svenpetersen1965/C64-PSU-Combi/Rev. 0/pictures/2509_-_Backside.JPG

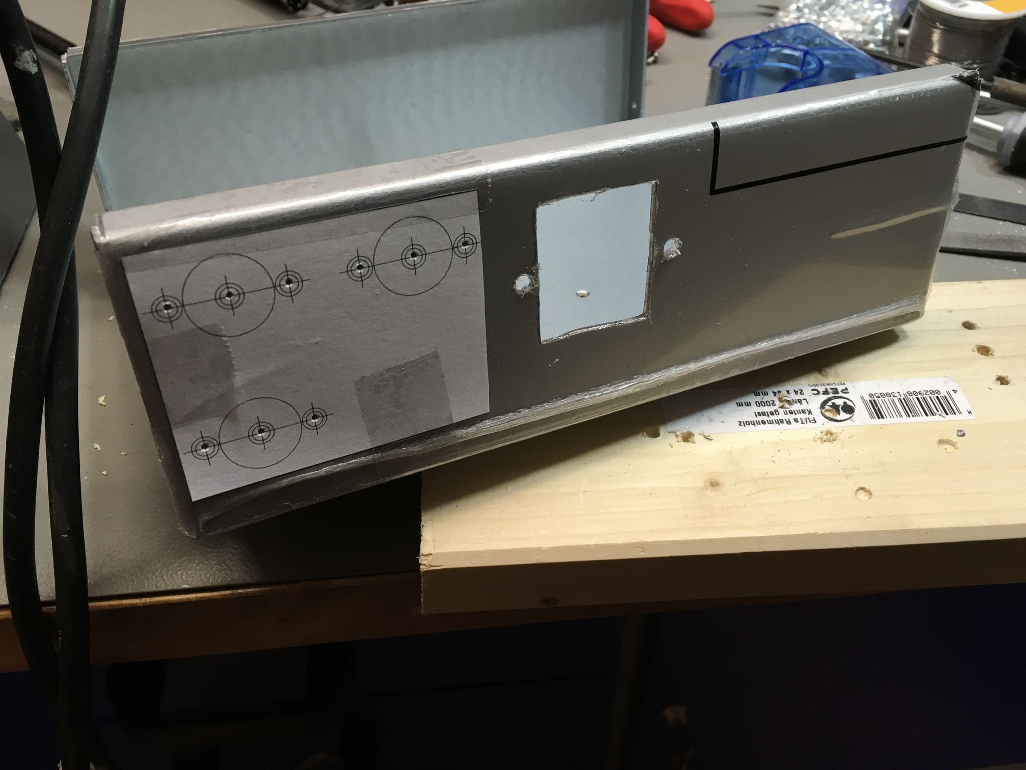
Rev. 0/pictures/2509_-_Backside.JPG
