svenpetersen1965/C64-PSU-Combi/Rev. 0/pictures/2510_-_crimp_tool.JPG

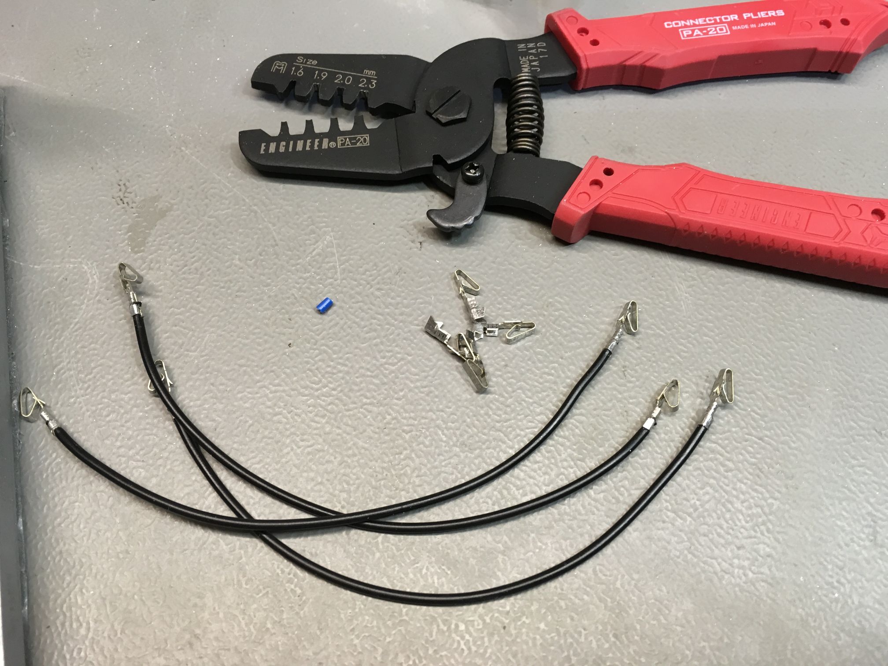
Rev. 0/pictures/2510_-_crimp_tool.JPG
