svenpetersen1965/C64-PSU-Combi/Rev. 0/pictures/2511_-_finished_PSU.JPG

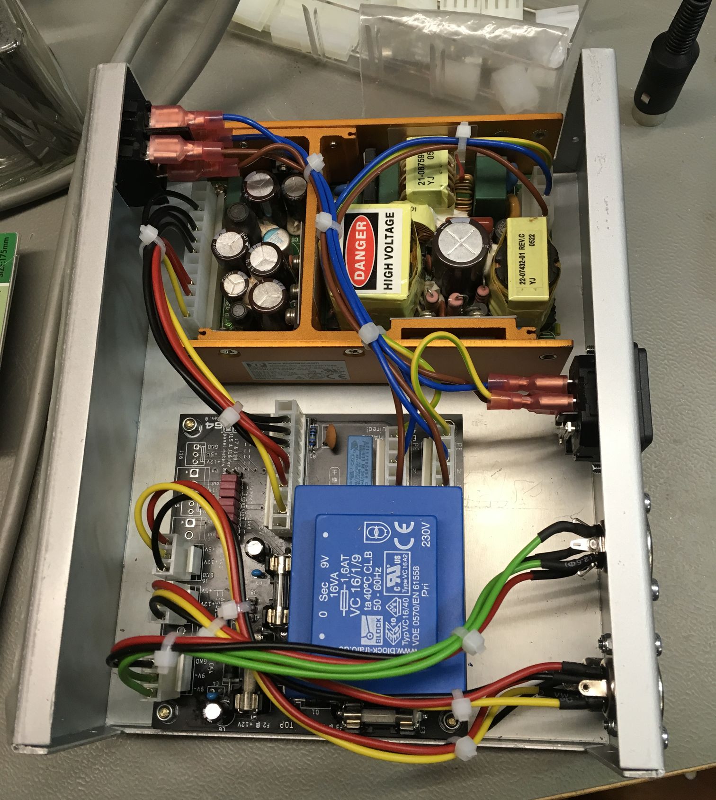
Rev. 0/pictures/2511_-_finished_PSU.JPG
