svenpetersen1965/C64-PSU-Combi/Rev. 0/pictures/2551_-_mounted_PCB.JPG

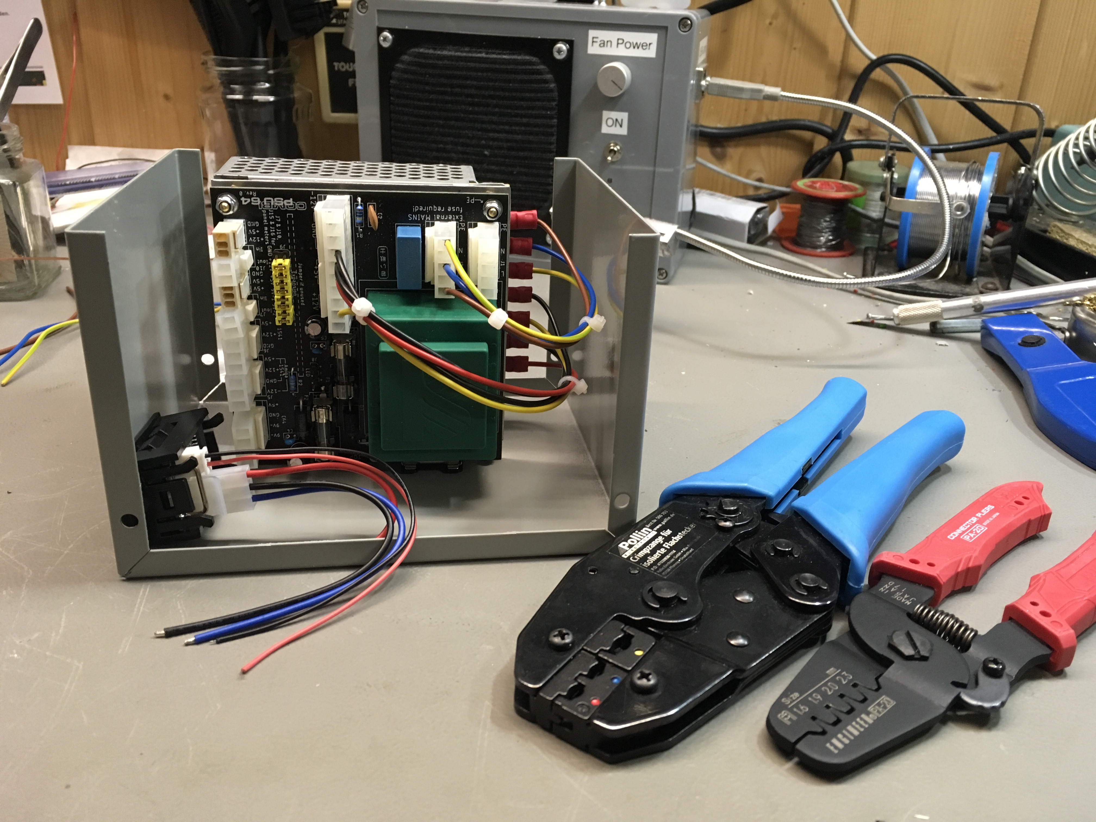
Rev. 0/pictures/2551_-_mounted_PCB.JPG
