svenpetersen1965/C64-PSU-Combi/Rev. 0/pictures/2552_-_mounted_RD_50A.JPG

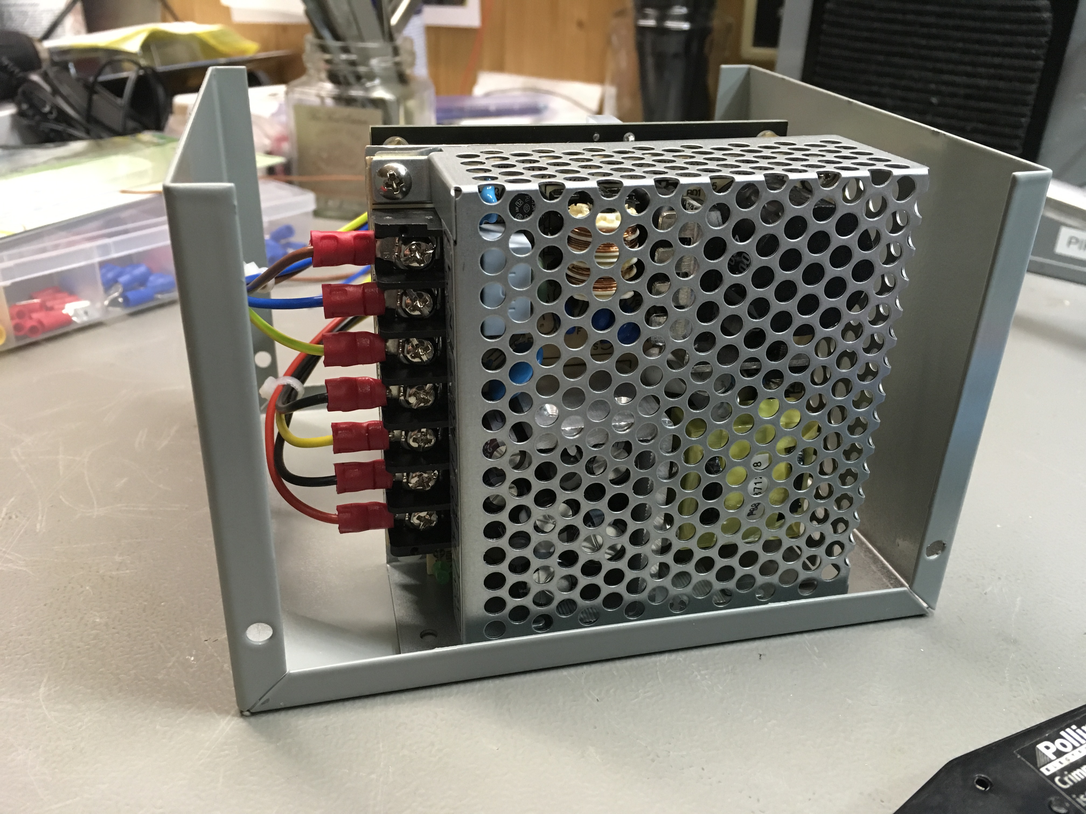
Rev. 0/pictures/2552_-_mounted_RD_50A.JPG
