svenpetersen1965/C64-PSU-Combi/Rev. 0/pictures/2553_-_panel_meters.JPG

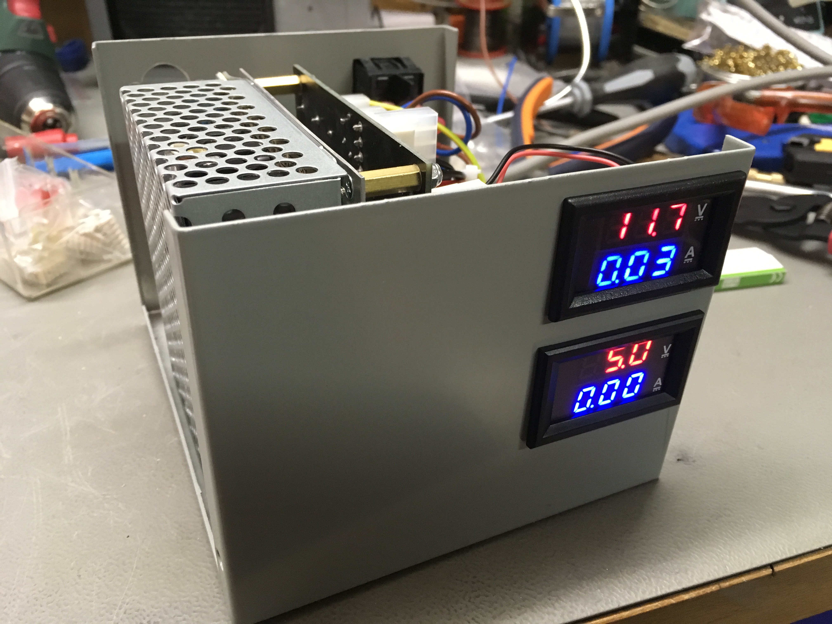
Rev. 0/pictures/2553_-_panel_meters.JPG
