svenpetersen1965/C64-PSU-Combi/Rev. 0/pictures/2554_-_Back_Side.JPG

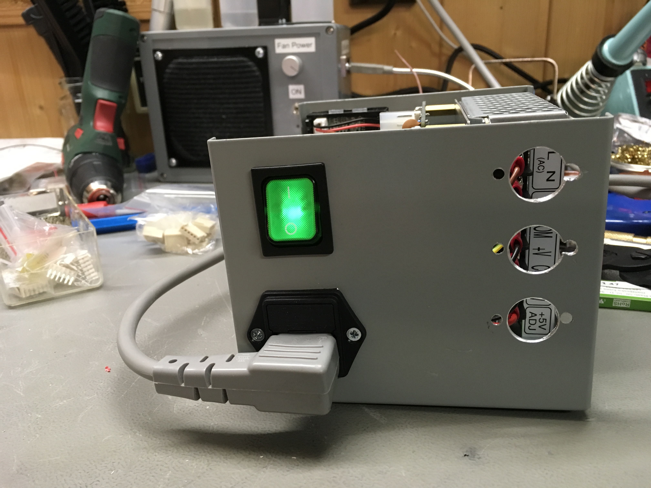
Rev. 0/pictures/2554_-_Back_Side.JPG
