svenpetersen1965/C64-PSU-Combi/Rev. 0/pictures/4061_-_RD50_Adj.JPG

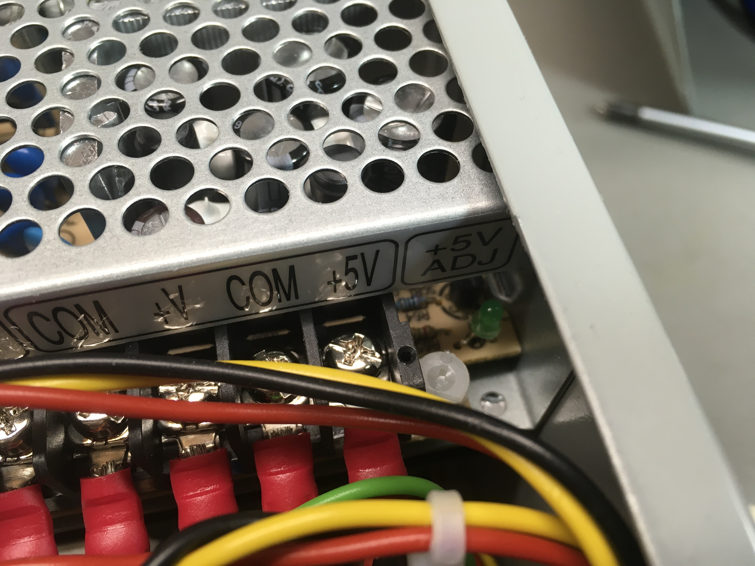
Rev. 0/pictures/4061_-_RD50_Adj.JPG
