svenpetersen1965/C64-PSU-Combi/Rev. 0/pictures/4064_-_bottom_side.JPG

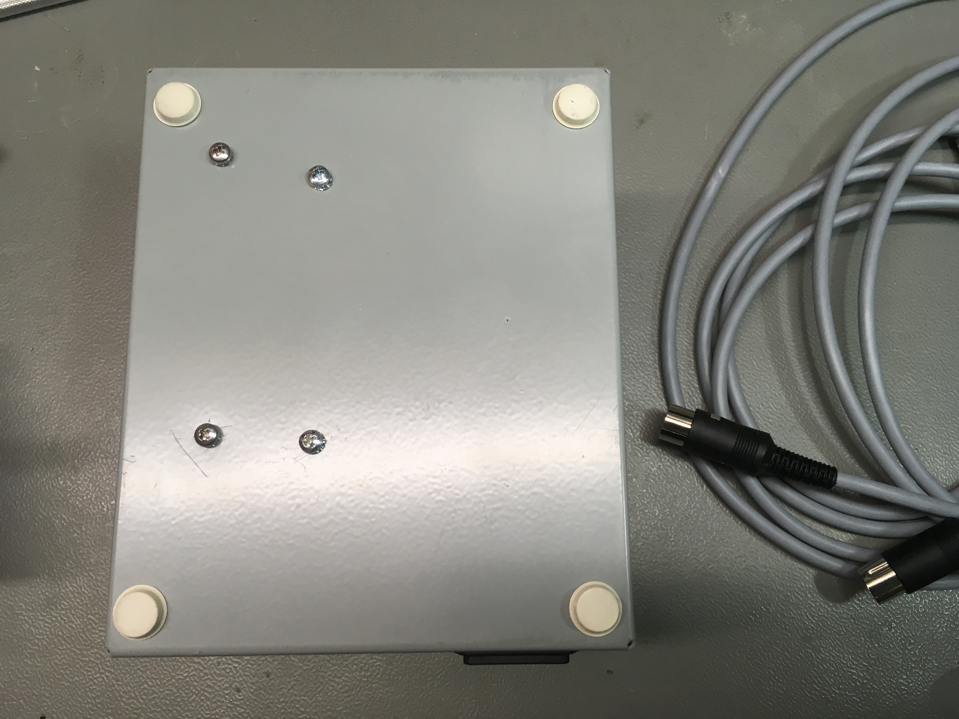
Rev. 0/pictures/4064_-_bottom_side.JPG
