svenpetersen1965/C64-PSU-Combi/Rev. 0/pictures/4066_-_fitting_panel.JPG

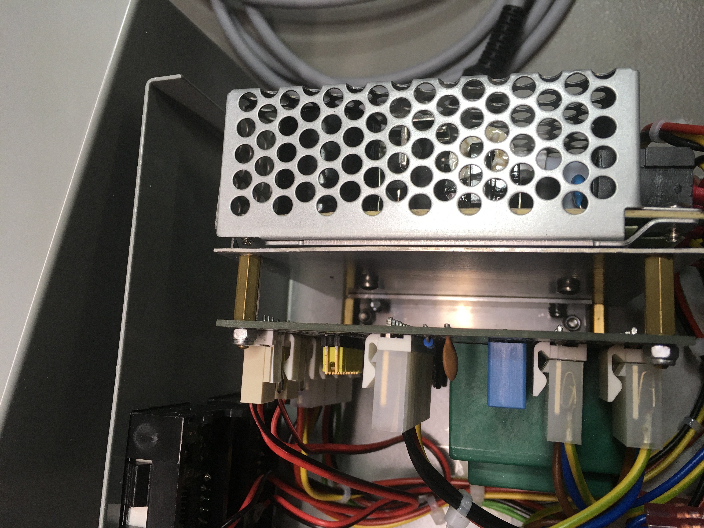
Rev. 0/pictures/4066_-_fitting_panel.JPG
