svenpetersen1965/C64-PSU-Combi/Rev. 1/pictures/C64_Combi_PSU_rev0_drawing.png

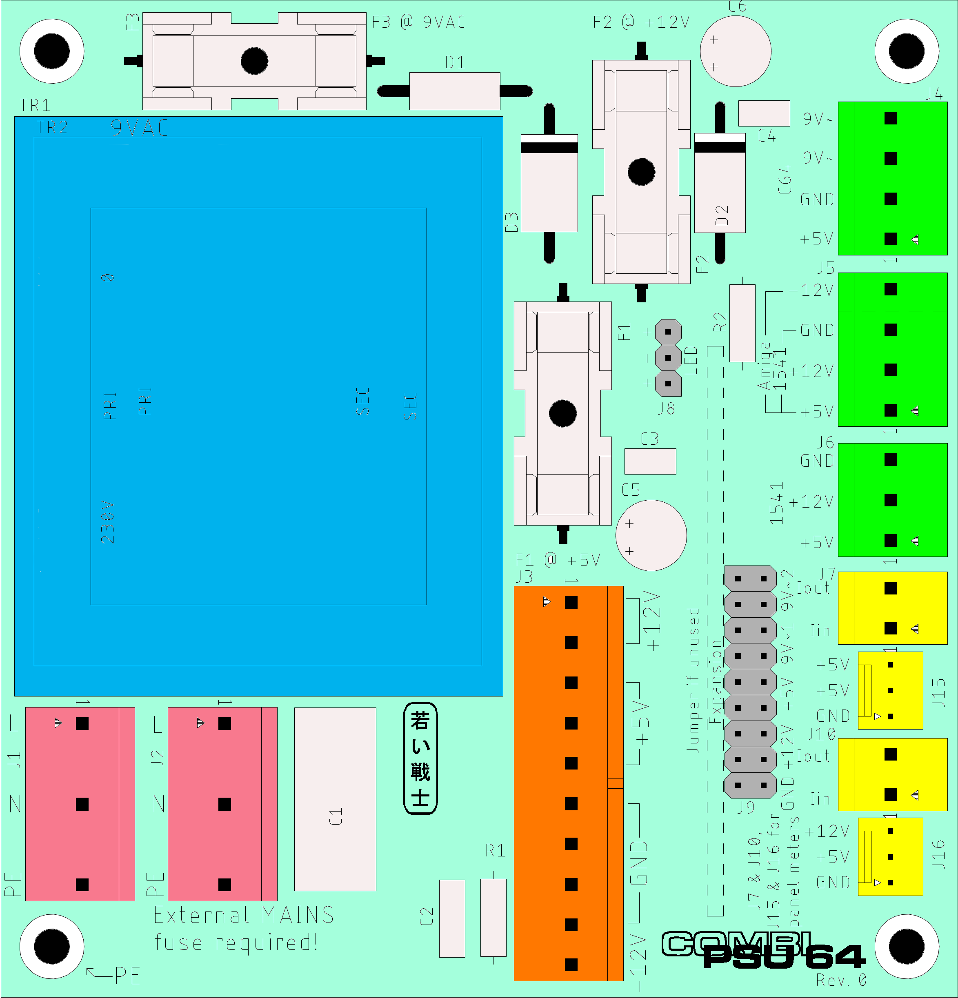
Rev. 1/pictures/C64_Combi_PSU_rev0_drawing.png
