svenpetersen1965/C64-PSU-Combi/Rev. 2/inkscape/rd-50.png

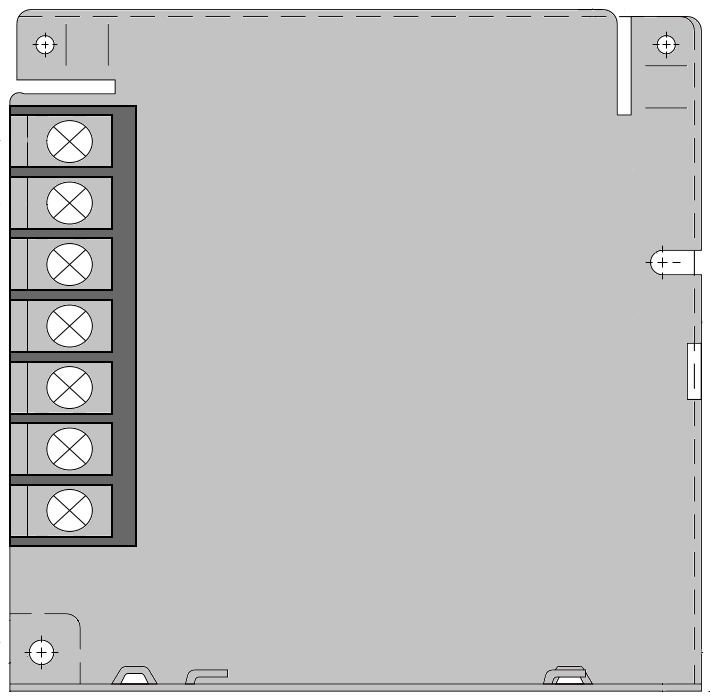
Rev. 2/inkscape/rd-50.png
