svenpetersen1965/C64-PSU-Combi/Rev. 2/pictures/4250_mounting_plate_top.JPG

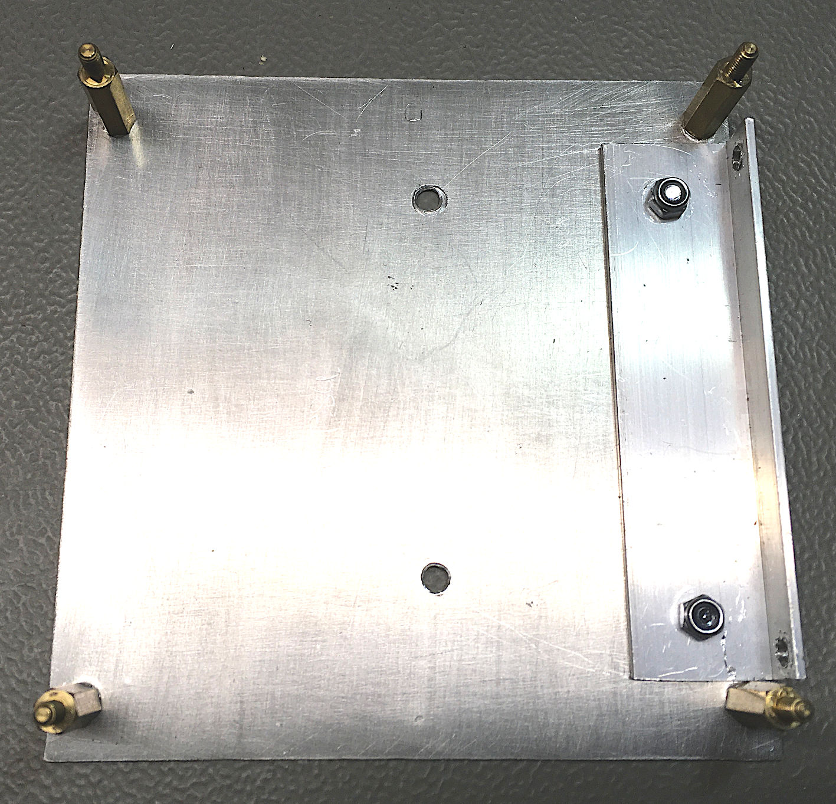
Rev. 2/pictures/4250_mounting_plate_top.JPG
