svenpetersen1965/C64-PSU-Combi/Rev. 2/pictures/4251_mounting_plate_bottom.JPG

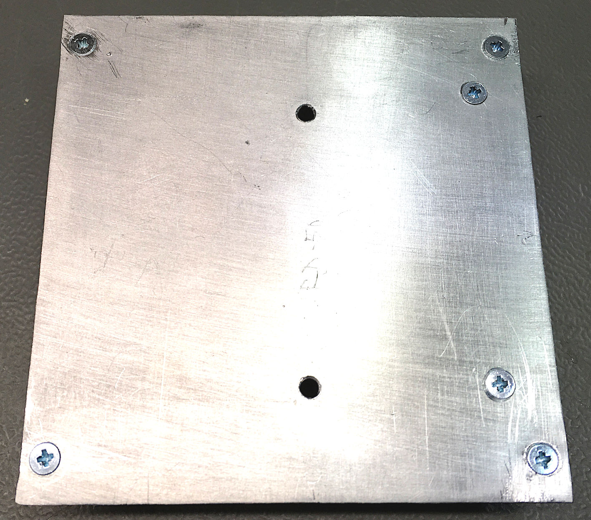
Rev. 2/pictures/4251_mounting_plate_bottom.JPG
