svenpetersen1965/C64-PSU-Combi/Rev. 2/pictures/4252_mounting_plate_dc_psu.JPG

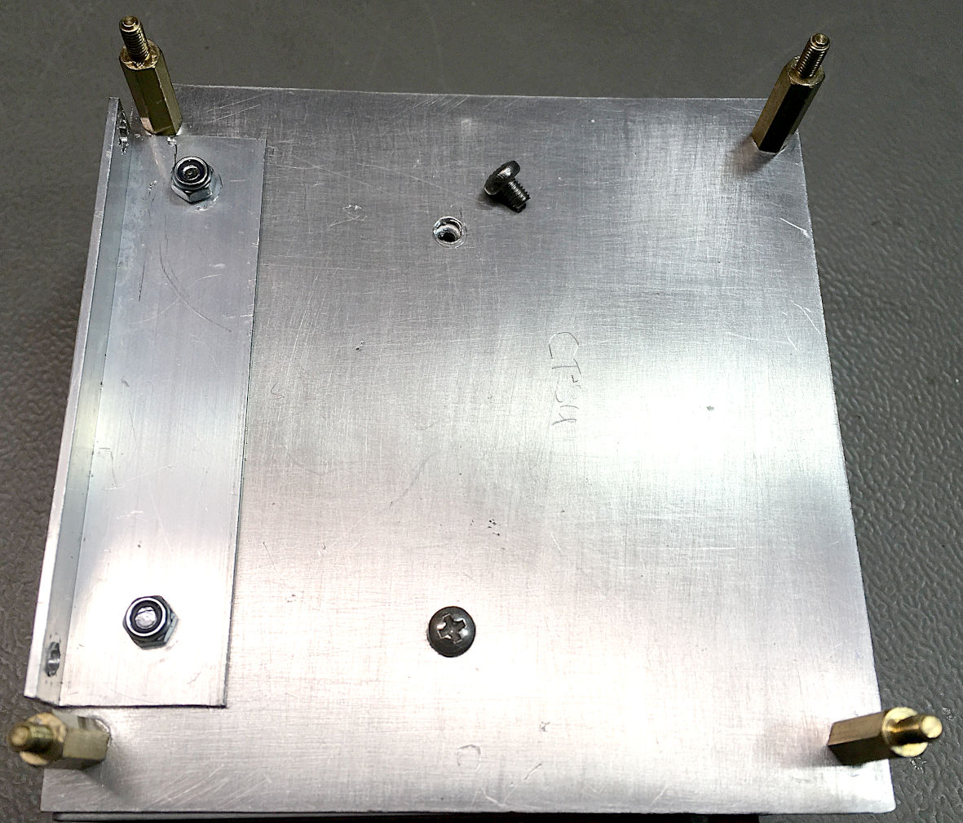
Rev. 2/pictures/4252_mounting_plate_dc_psu.JPG
