svenpetersen1965/C64-PSU-Combi/Rev. 2/pictures/4255_back_panel_half.JPG

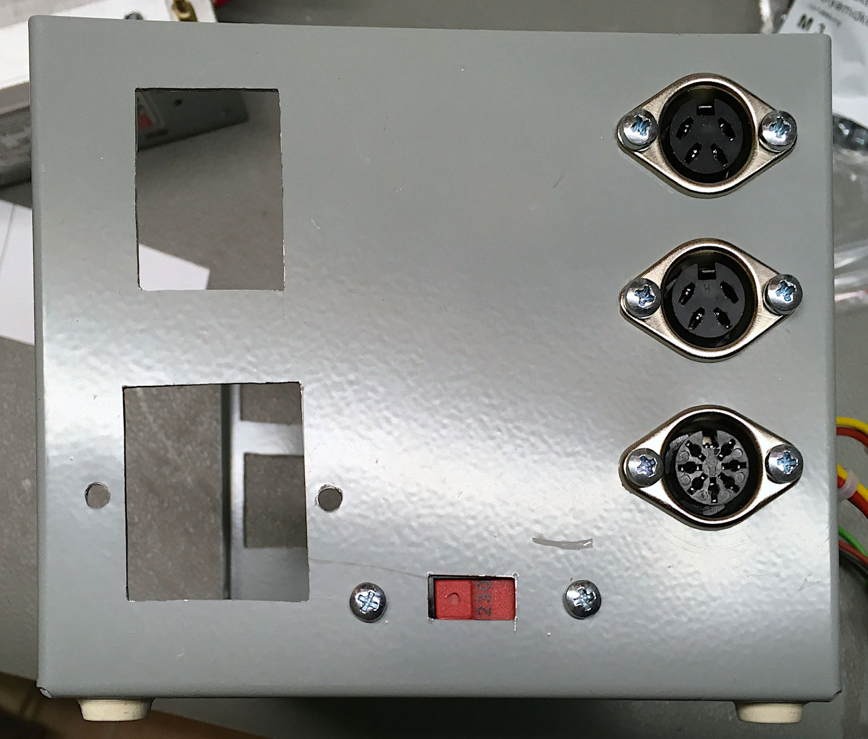
Rev. 2/pictures/4255_back_panel_half.JPG
