svenpetersen1965/C64-PSU-Combi/Rev. 2/pictures/4259_back_panel_full.JPG

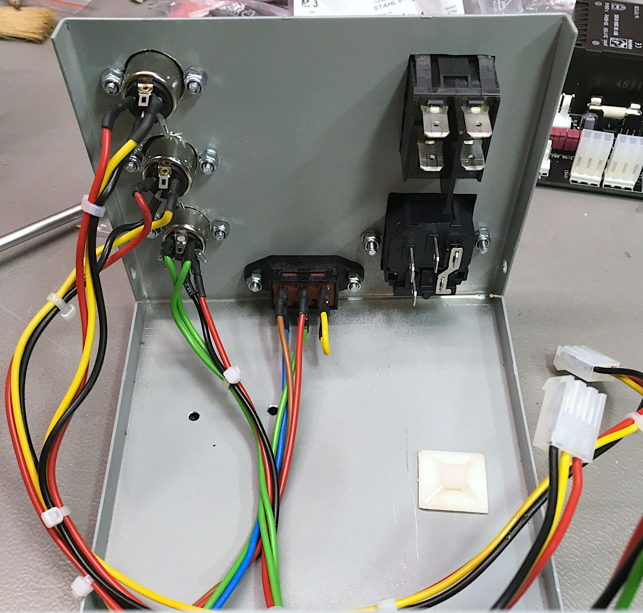
Rev. 2/pictures/4259_back_panel_full.JPG
