svenpetersen1965/C64-PSU-Combi/Rev. 2/pictures/4260_dc_psu_w300_w500.JPG

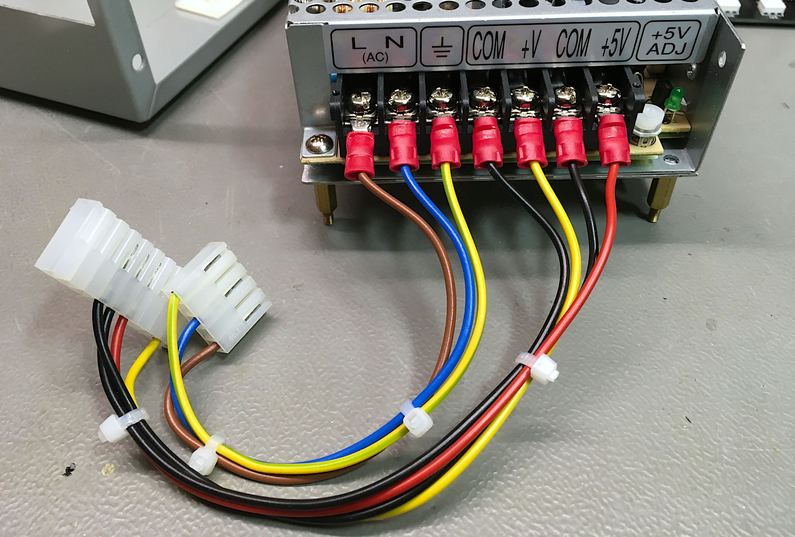
Rev. 2/pictures/4260_dc_psu_w300_w500.JPG
