svenpetersen1965/C64-PSU-Combi/Rev. 2/pictures/4261_dc_psu_mounted.JPG

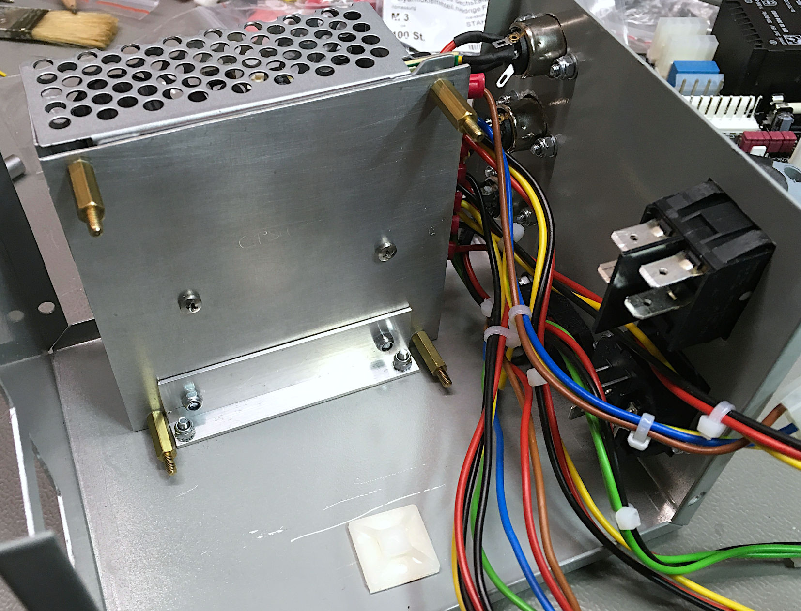
Rev. 2/pictures/4261_dc_psu_mounted.JPG
