svenpetersen1965/C64-PSU-Combi/Rev. 2/pictures/4274_T1_T2.JPG

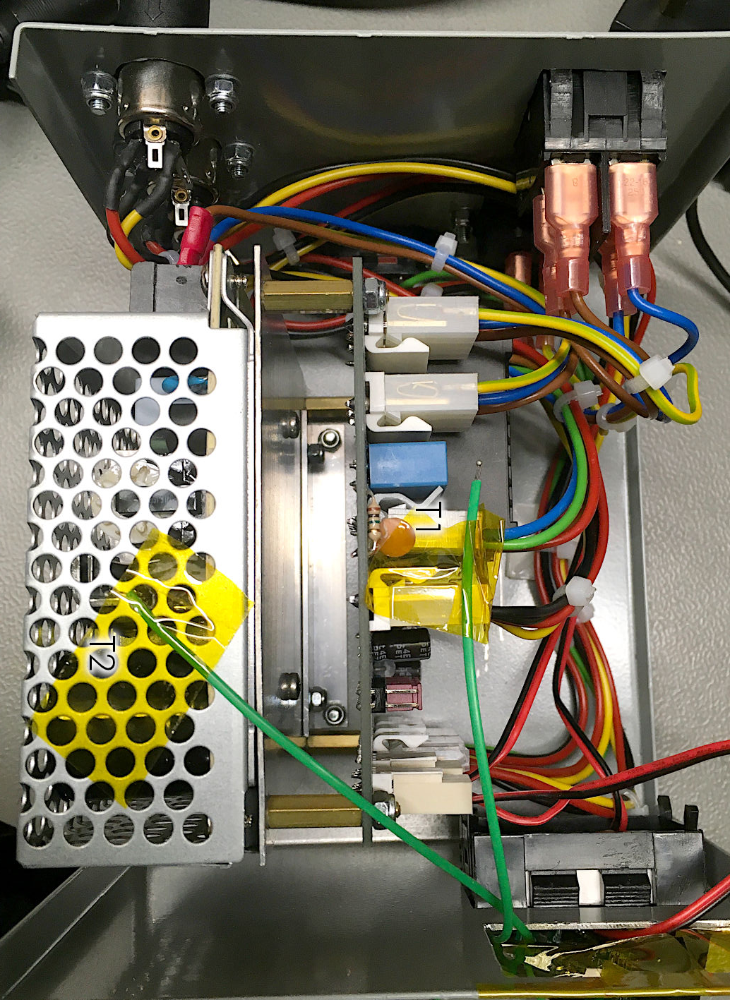
Rev. 2/pictures/4274_T1_T2.JPG
