svenpetersen1965/C64-PSU-Combi/Rev. 2/pictures/4286_115V_mains.JPG

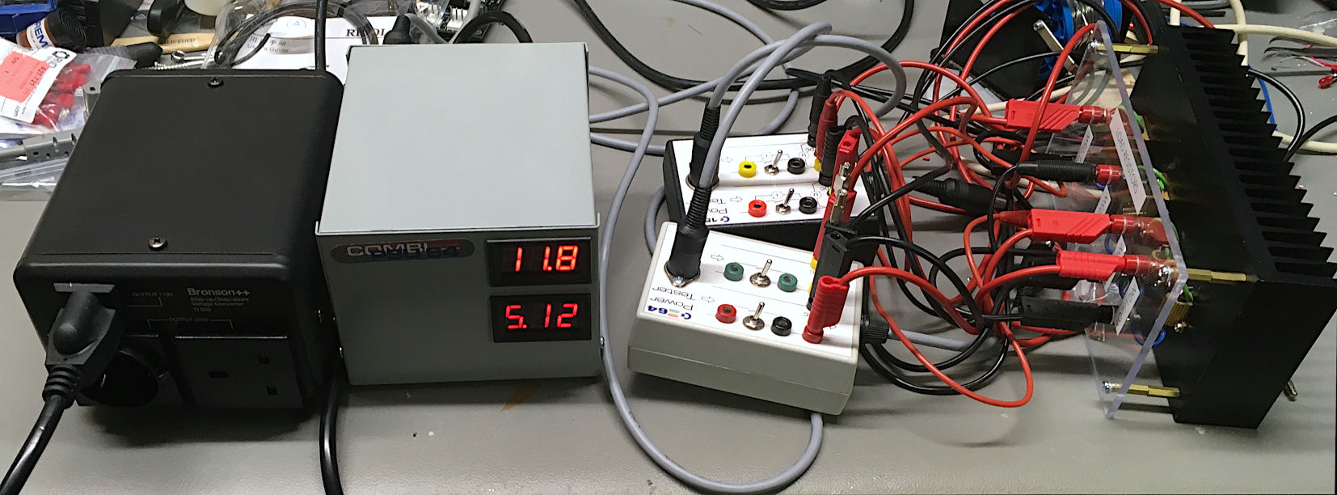
Rev. 2/pictures/4286_115V_mains.JPG
