svenpetersen1965/C64-PSU-Combi/Rev. 2/pictures/4297_PCB_two_versions.JPG

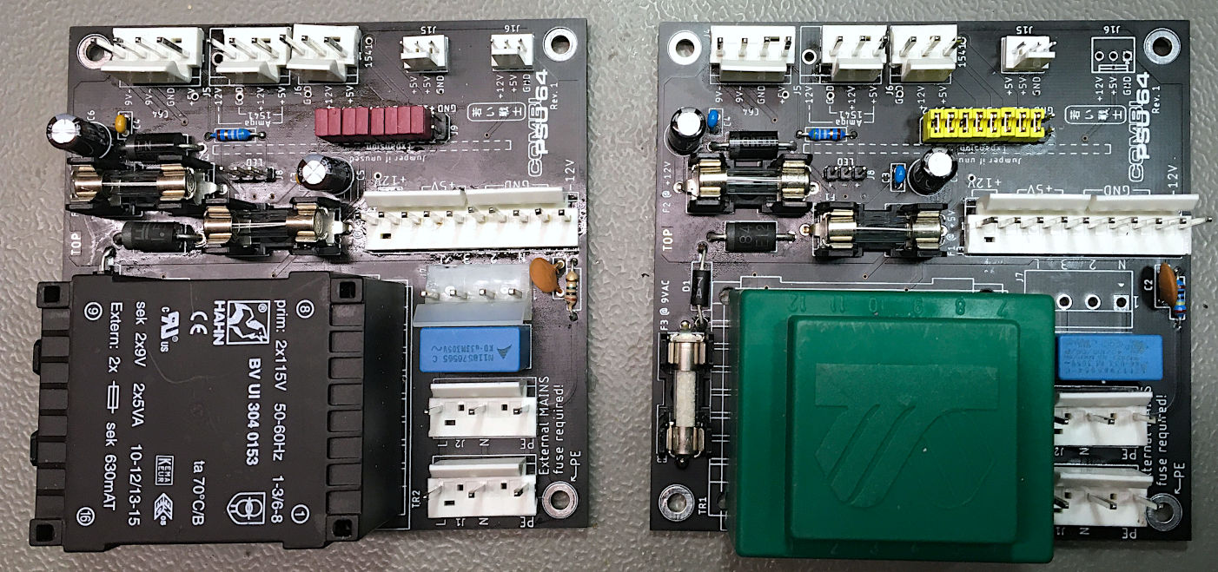
Rev. 2/pictures/4297_PCB_two_versions.JPG
