svenpetersen1965/C64-PSU-Combi/Rev. 2/pictures/4299_PCB_mounted.JPG

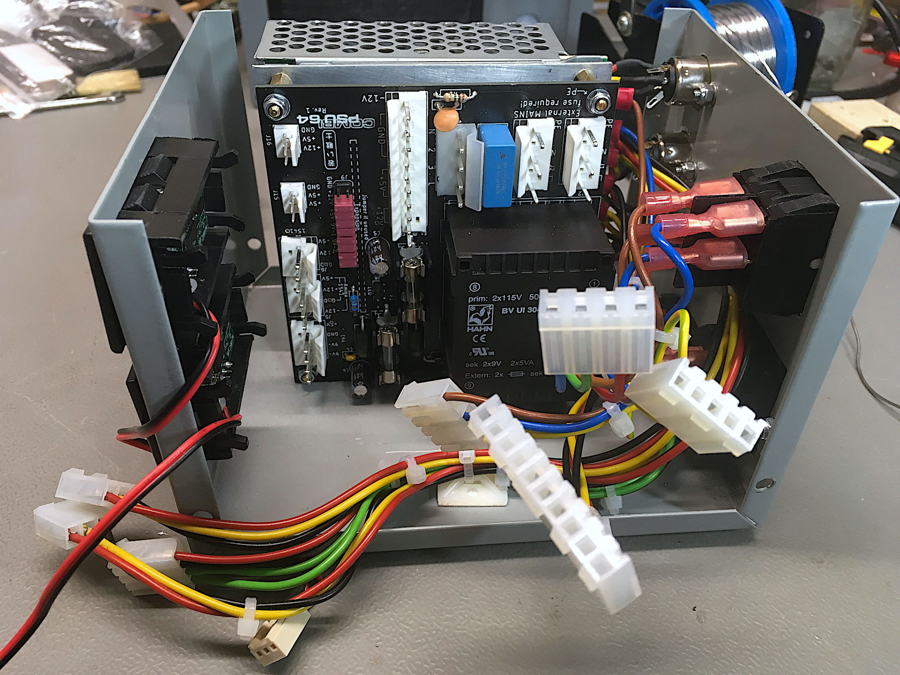
Rev. 2/pictures/4299_PCB_mounted.JPG
