svenpetersen1965/C64-PSU-Combi/Rev. 2/pictures/4335_W100.JPG

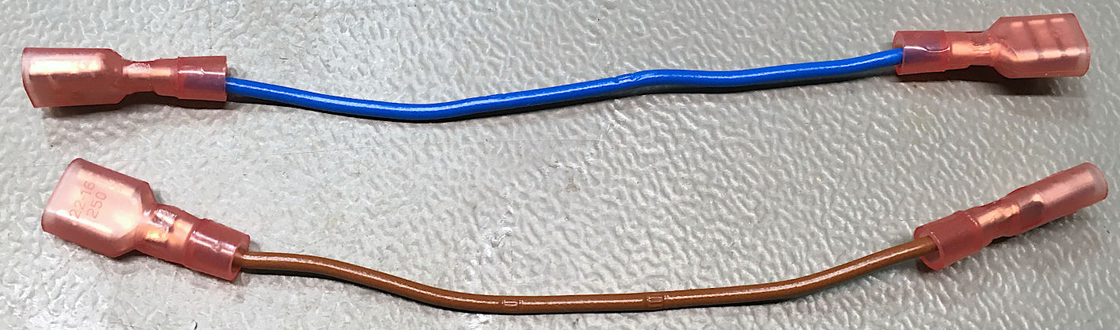
Rev. 2/pictures/4335_W100.JPG
