svenpetersen1965/C64-PSU-Combi/Rev. 2/pictures/4336_W200.JPG

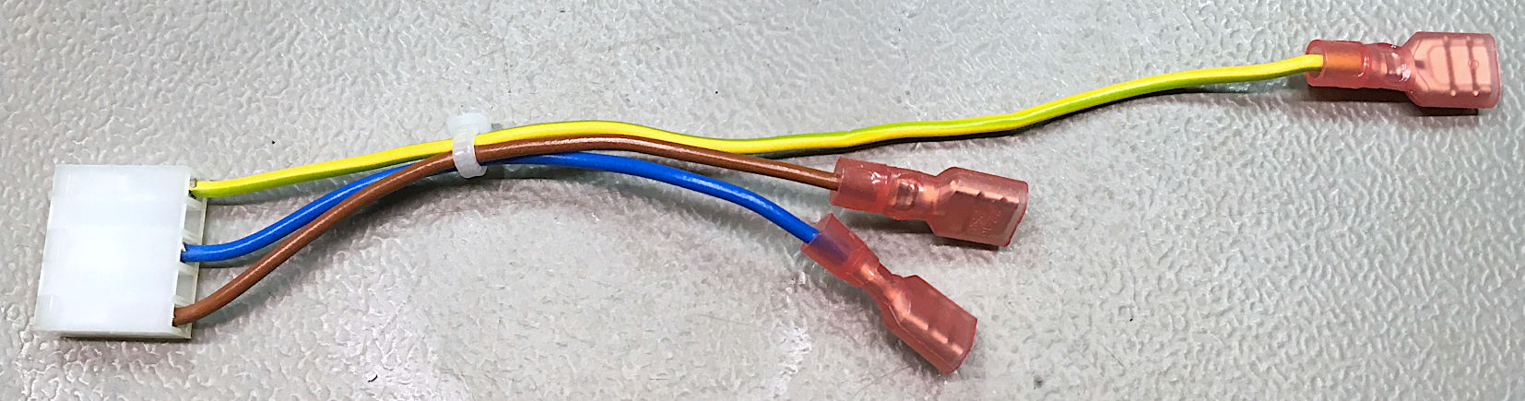
Rev. 2/pictures/4336_W200.JPG
