svenpetersen1965/C64-PSU-Combi/Rev. 2/pictures/4337_W300.JPG

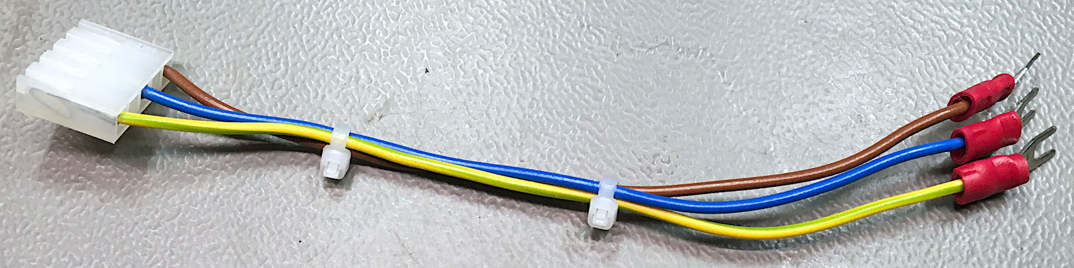
Rev. 2/pictures/4337_W300.JPG
