svenpetersen1965/C64-PSU-Combi/Rev. 2/pictures/4338_W400.JPG

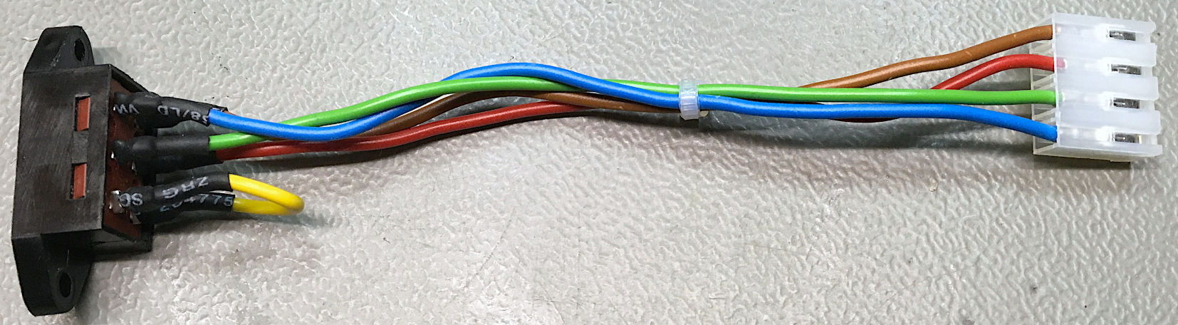
Rev. 2/pictures/4338_W400.JPG
