svenpetersen1965/C64-PSU-Combi/Rev. 2/pictures/4339_W400_detail.JPG

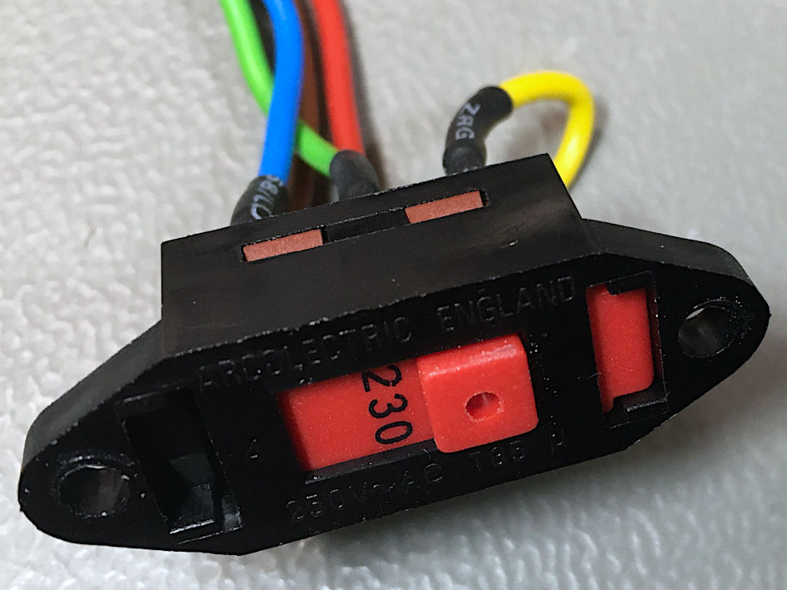
Rev. 2/pictures/4339_W400_detail.JPG
