svenpetersen1965/C64-PSU-Combi/Rev. 2/pictures/4342_W500.JPG

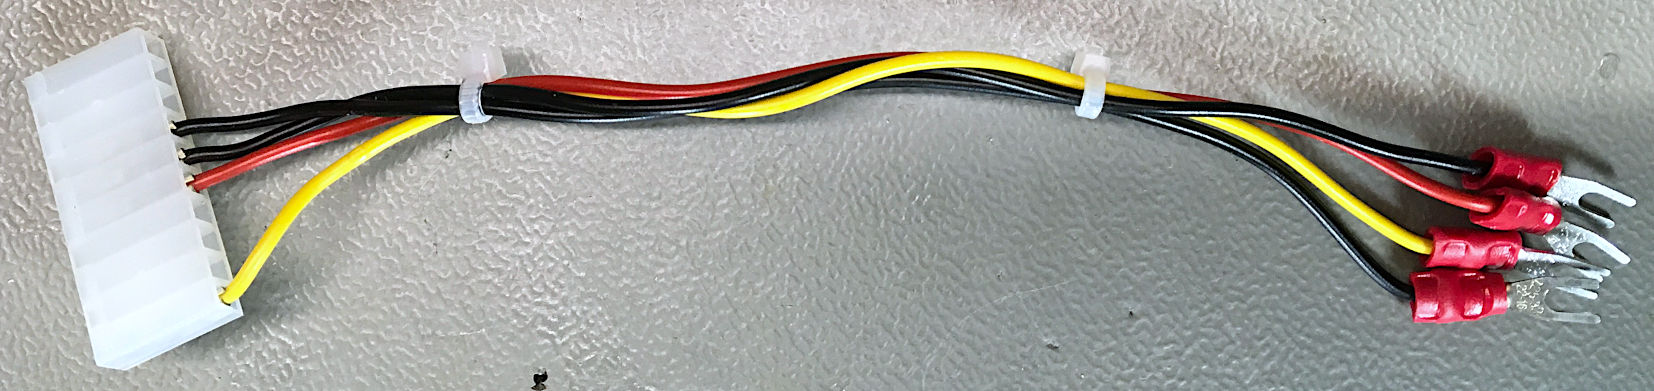
Rev. 2/pictures/4342_W500.JPG
