svenpetersen1965/C64-PSU-Combi/Rev. 2/pictures/4343_W600.JPG

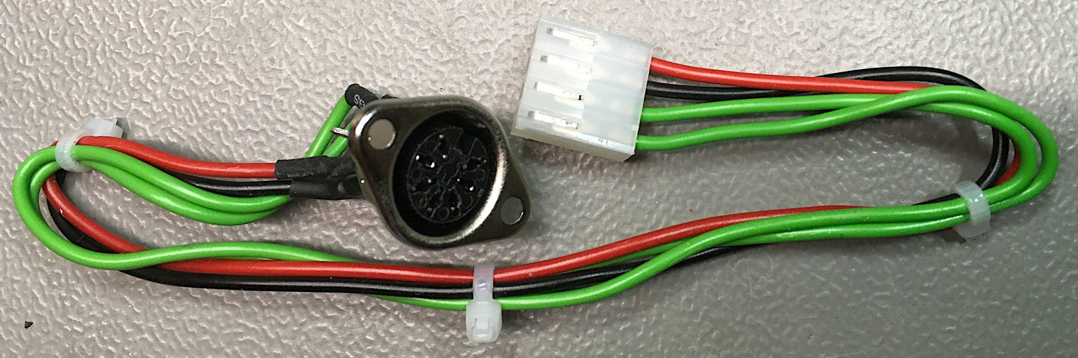
Rev. 2/pictures/4343_W600.JPG
