svenpetersen1965/C64-PSU-Combi/Rev. 2/pictures/4344_W700.JPG

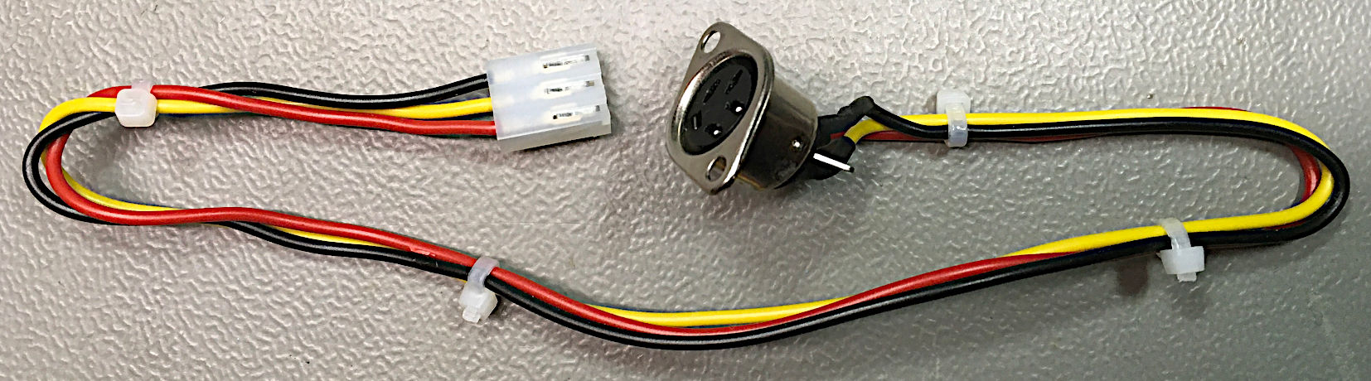
Rev. 2/pictures/4344_W700.JPG
