svenpetersen1965/C64-PSU-Combi/Rev. 2/pictures/4346_W700_detail.JPG

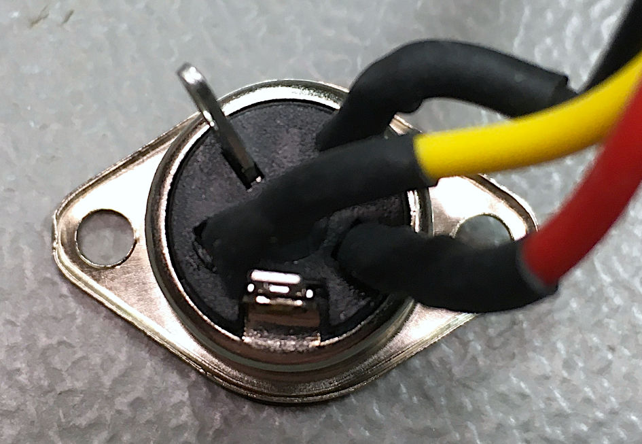
Rev. 2/pictures/4346_W700_detail.JPG
