svenpetersen1965/C64-PSU-Combi/Rev. 2/pictures/4348_W600_detail.JPG

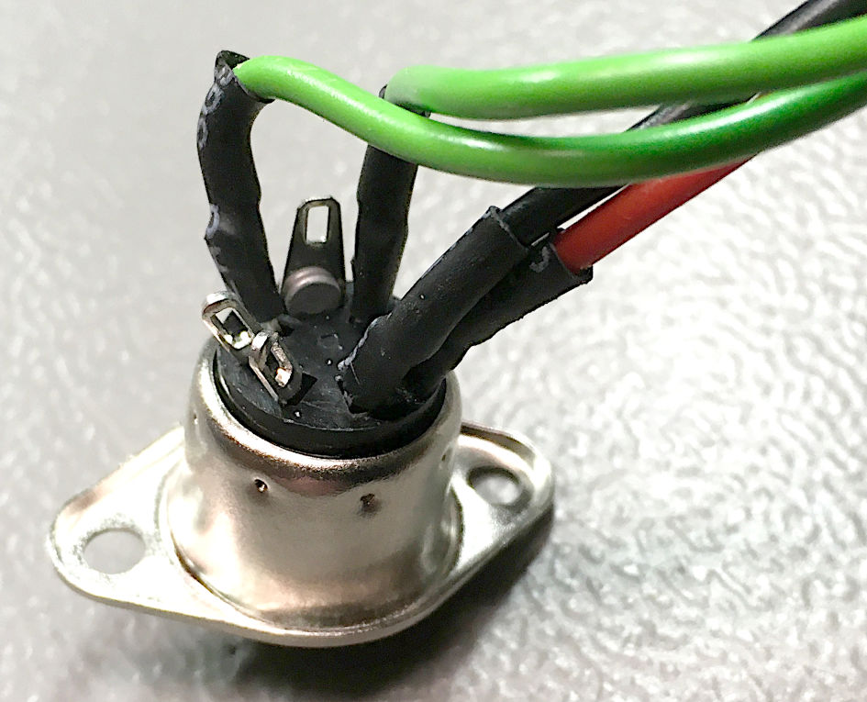
Rev. 2/pictures/4348_W600_detail.JPG
