svenpetersen1965/C64-PSU-Combi/Rev. 2/pictures/4349_W900.JPG

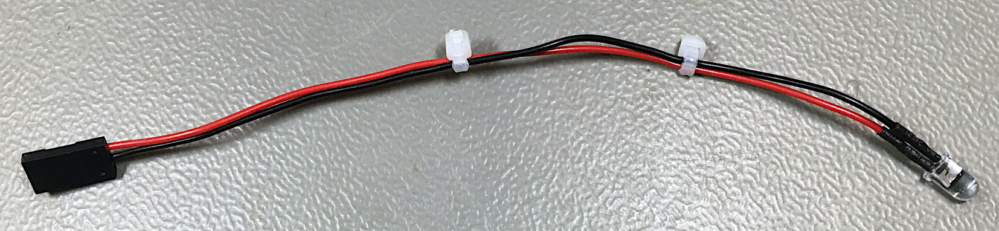
Rev. 2/pictures/4349_W900.JPG
