svenpetersen1965/C64-PSU-Combi/Rev. 2/pictures/4439_mains_switch_connector.JPG

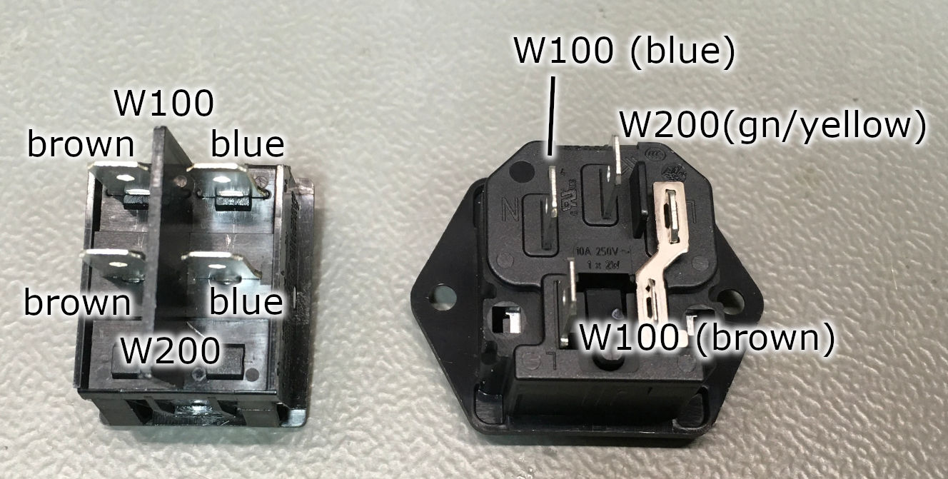
Rev. 2/pictures/4439_mains_switch_connector.JPG
