svenpetersen1965/C64-PSU-Combi/Rev. 2/pictures/brd_rev2.png

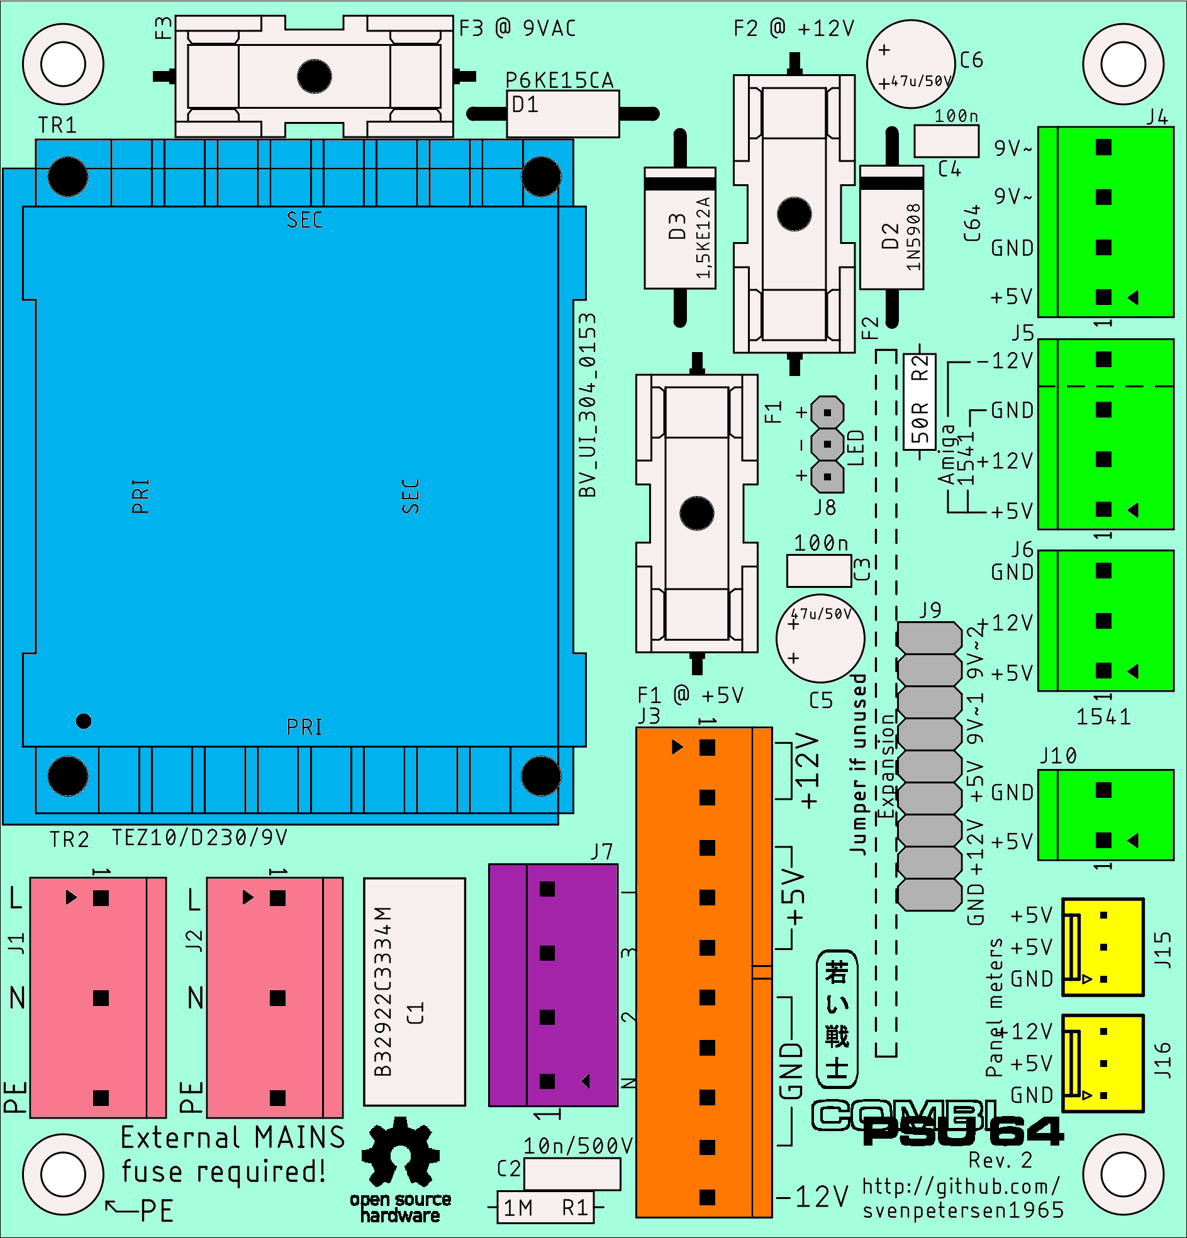
Rev. 2/pictures/brd_rev2.png
