svenpetersen1965/C64-PSU-Combi/Rev. 2/pictures/dimensions.png

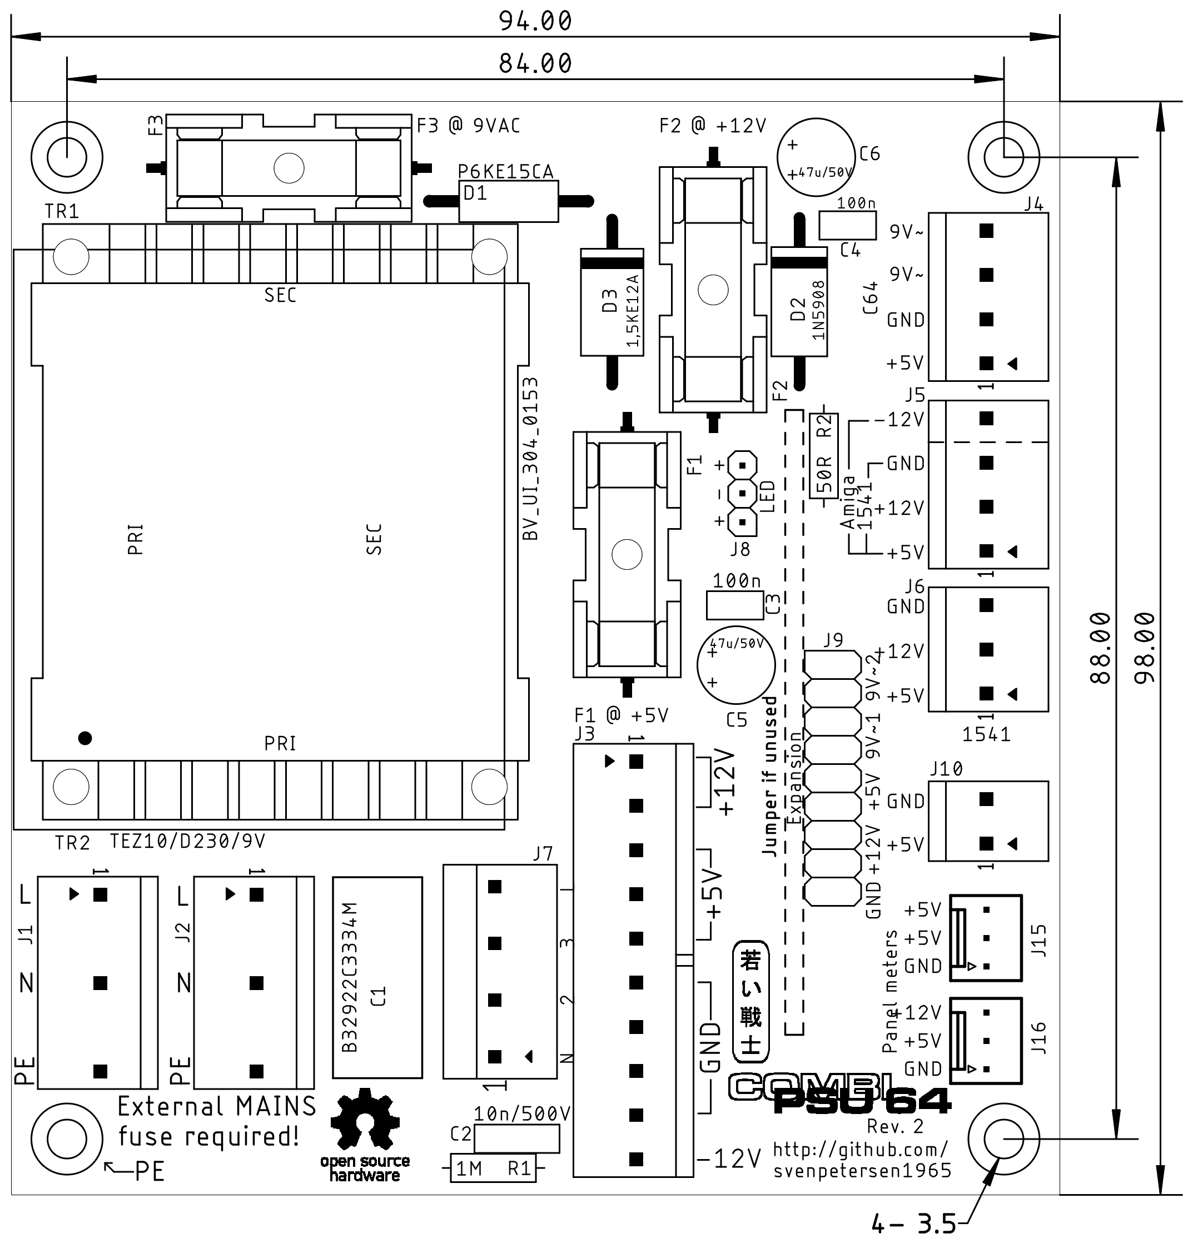
Rev. 2/pictures/dimensions.png
