svenpetersen1965/C64-PSU-Combi/Rev. 2/pictures/FLIR_20200402-140658.jpg

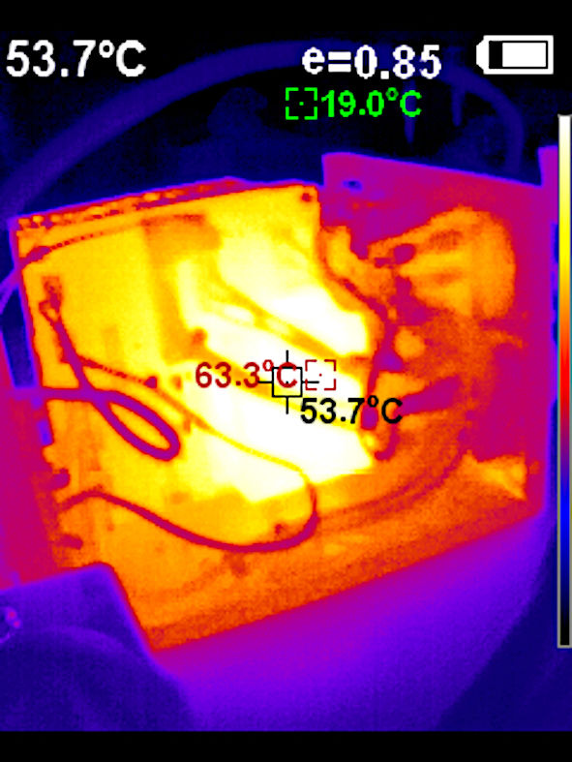
Rev. 2/pictures/FLIR_20200402-140658.jpg
