svenpetersen1965/C64-PSU-Combi/Rev. 2/pictures/FLIR_PSU_combi.jpg

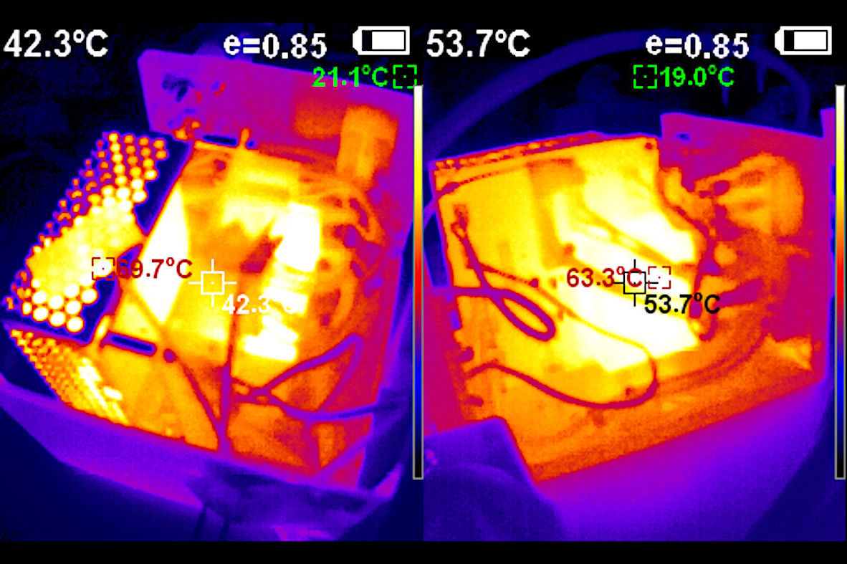
Rev. 2/pictures/FLIR_PSU_combi.jpg
