svenpetersen1965/C64-PSU-Combi/Rev. 2/pictures/LED_marking.png

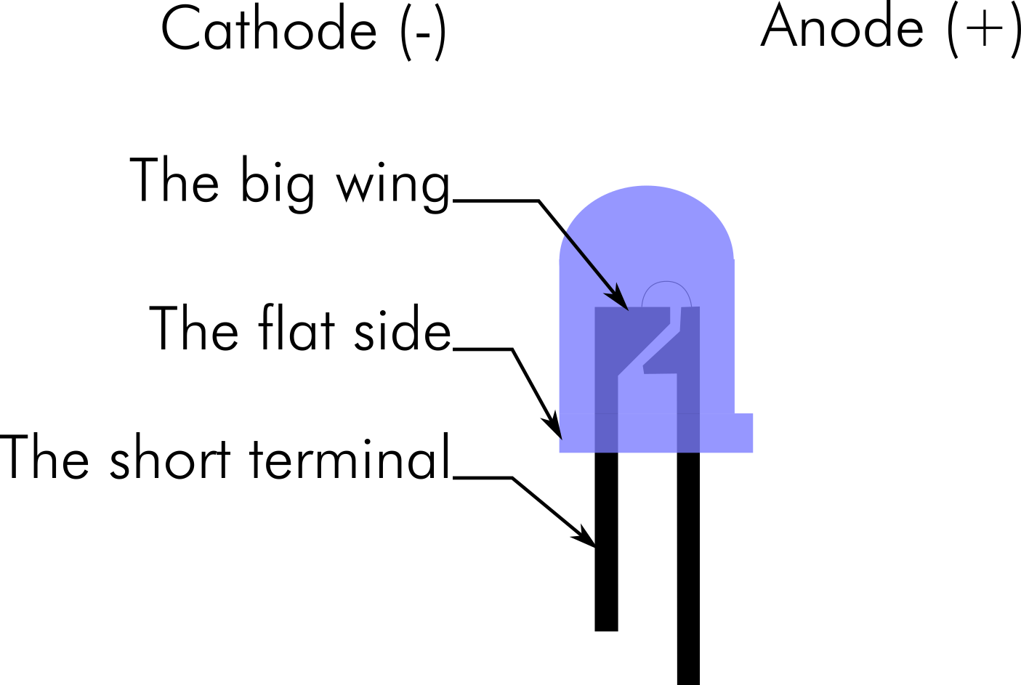
Rev. 2/pictures/LED_marking.png
