svenpetersen1965/C64-PSU-Combi/Rev. 2/pictures/mains switch.jpg

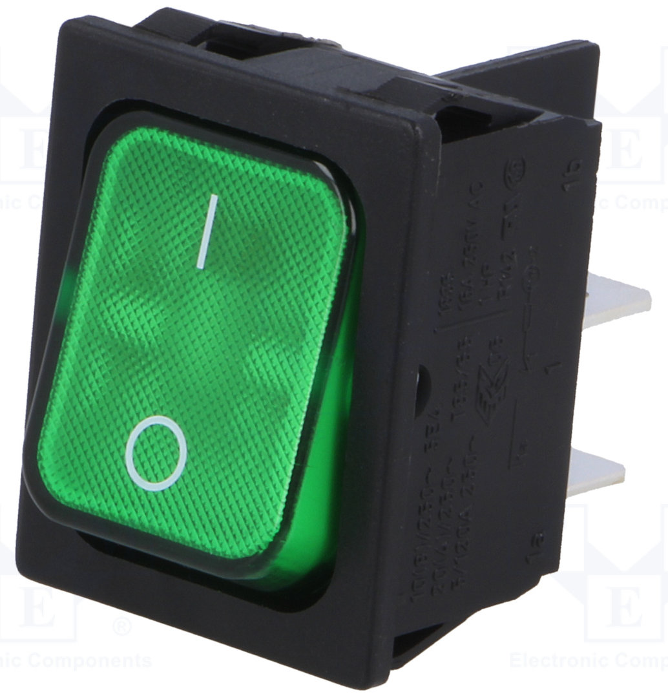
Rev. 2/pictures/mains switch.jpg
