svenpetersen1965/C64-PSU-Combi/Rev. 2/pictures/mains_voltage_selector.png

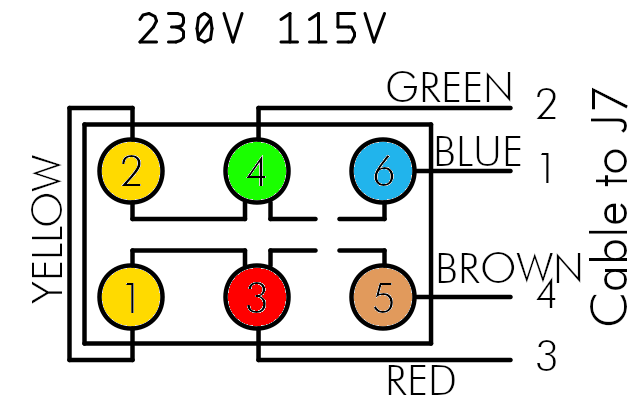
Rev. 2/pictures/mains_voltage_selector.png
