svenpetersen1965/C64-PSU-Combi/Rev. 2/pictures/Scope_5VDC_200us.png

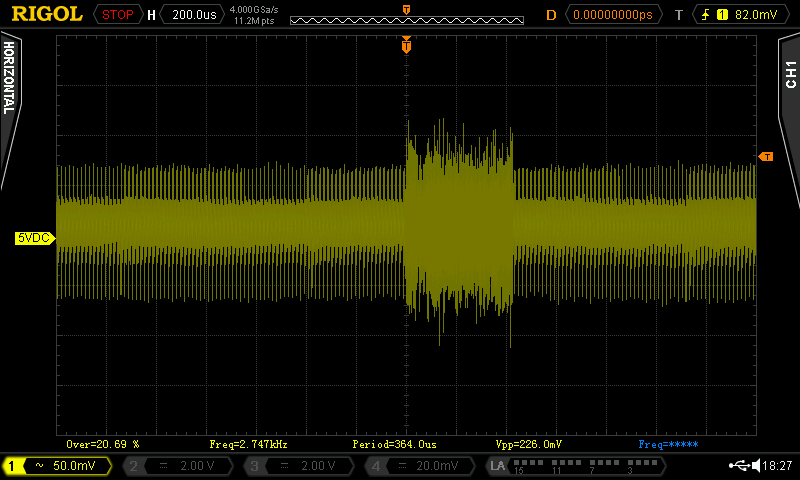
Rev. 2/pictures/Scope_5VDC_200us.png
