svenpetersen1965/C64-PSU-Combi/Rev. 2/pictures/Scope_9VAC.png

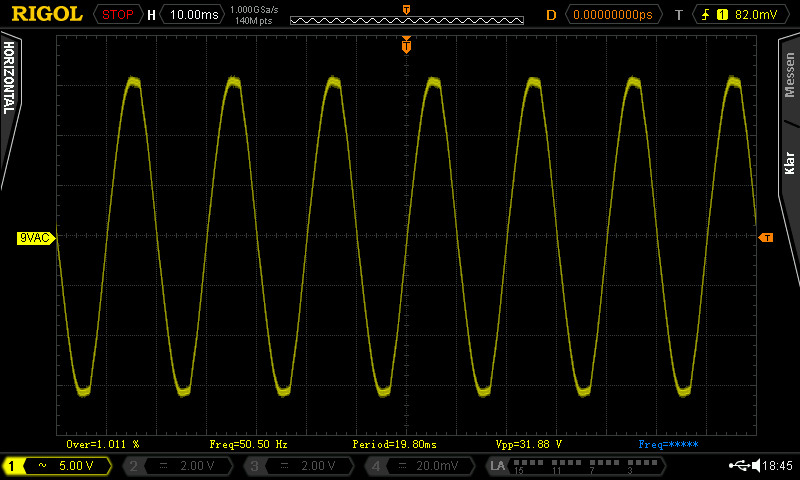
Rev. 2/pictures/Scope_9VAC.png
