svenpetersen1965/C64-PSU-Combi/Rev. 2/pictures/Scope_12VDC_500us.png

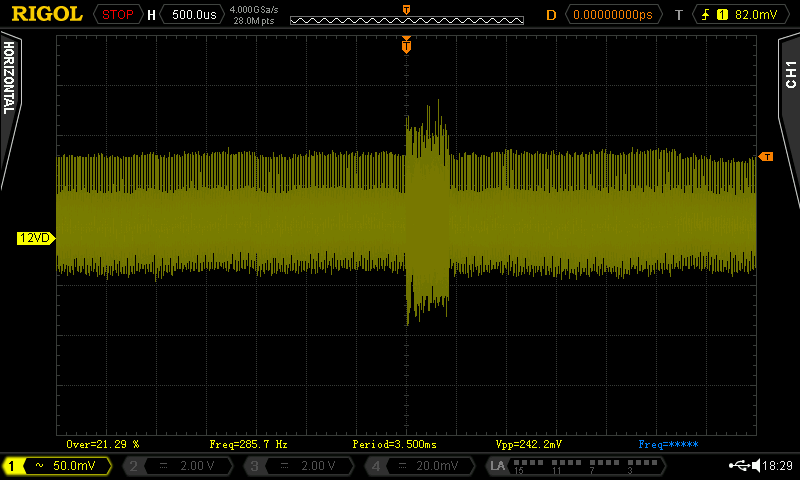
Rev. 2/pictures/Scope_12VDC_500us.png
